simi1505/60W-2m-FM-TRX-OE3SDE/1W FM TRX DRA818V/Eagle Files/1W_FM_TRX_DRA818V_Pics/1W FM TRX DRA818V_Drills.png

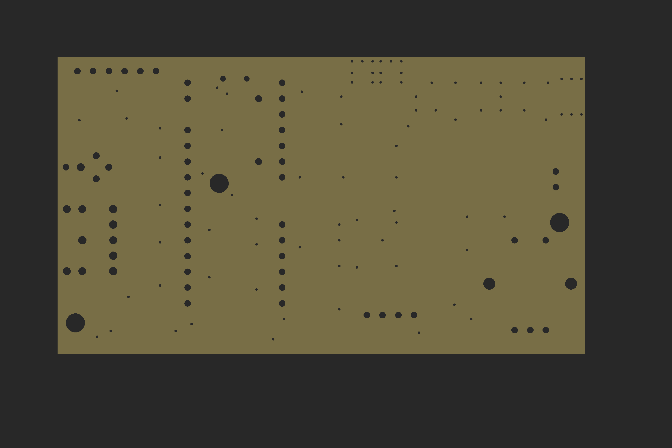
1W FM TRX DRA818V/Eagle Files/1W_FM_TRX_DRA818V_Pics/1W FM TRX DRA818V_Drills.png
