simi1505/60W-2m-FM-TRX-OE3SDE/60W FM PA RA60H1317M1A/Eagle Files/60W_FM_PA_Pics/60W_FM_PA_Drills.png

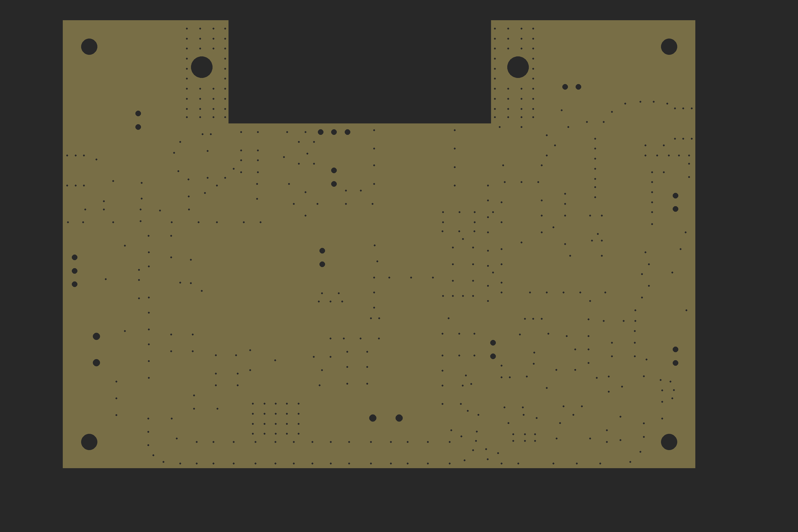
60W FM PA RA60H1317M1A/Eagle Files/60W_FM_PA_Pics/60W_FM_PA_Drills.png
