simi1505/60W-2m-FM-TRX-OE3SDE/60W FM PA RA60H1317M1A/Simulation/Elsie/LC-BP-IN/BPF1_Circuit.PNG

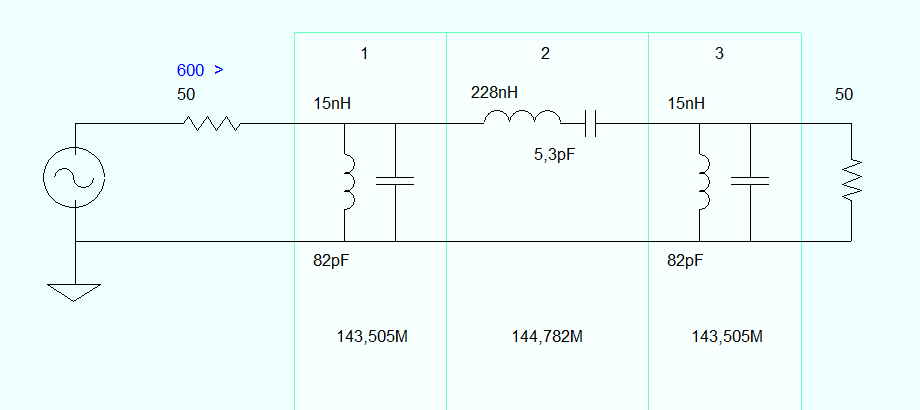
60W FM PA RA60H1317M1A/Simulation/Elsie/LC-BP-IN/BPF1_Circuit.PNG
