simi1505/60W-2m-FM-TRX-OE3SDE/60W FM PA RA60H1317M1A/Simulation/Elsie/LC-LP-OUT/LC-LP-OUT_Circuit.PNG

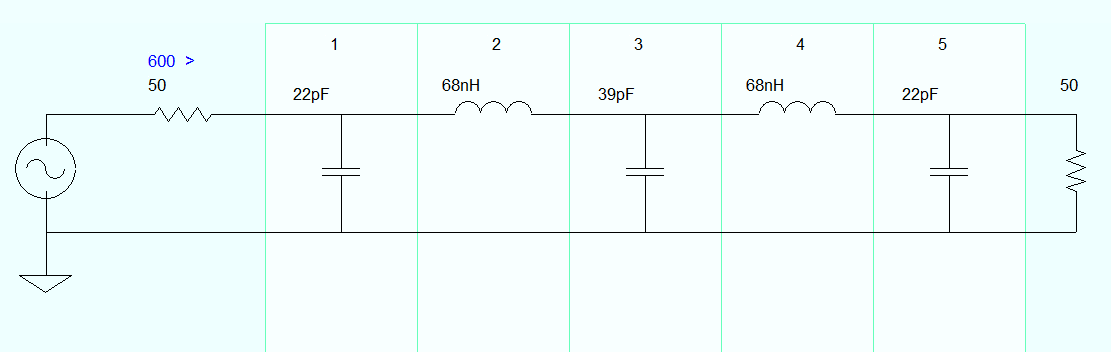
60W FM PA RA60H1317M1A/Simulation/Elsie/LC-LP-OUT/LC-LP-OUT_Circuit.PNG
