simi1505/60W-2m-FM-TRX-OE3SDE/60W FM PA RA60H1317M1A/Simulation/LTSpice/LC-LP-OUT/LC-LP_OUT.PNG

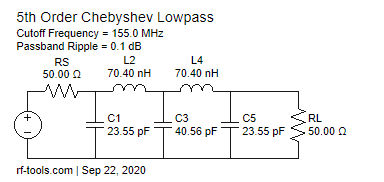
60W FM PA RA60H1317M1A/Simulation/LTSpice/LC-LP-OUT/LC-LP_OUT.PNG
