simi1505/60W-2m-FM-TRX-OE3SDE/60W FM PA RA60H1317M1A/Documentation/8_result/fig/result_2.jpg

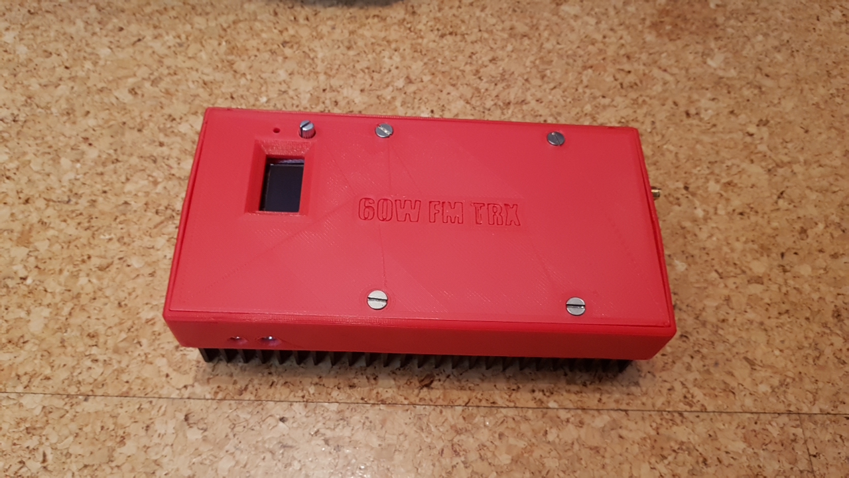
60W FM PA RA60H1317M1A/Documentation/8_result/fig/result_2.jpg
