simi1505/60W-2m-FM-TRX-OE3SDE/60W FM PA RA60H1317M1A/Documentation/8_result/fig/WhatsApp Image 2021-08-19 at 13.19.44 (3).jpeg

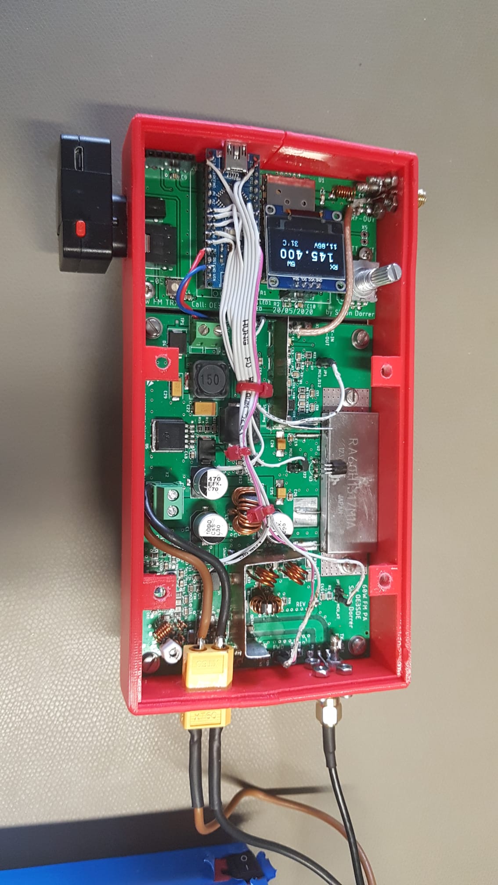
60W FM PA RA60H1317M1A/Documentation/8_result/fig/WhatsApp Image 2021-08-19 at 13.19.44 (3).jpeg
