simi1505/60W-2m-FM-TRX-OE3SDE/60W FM PA RA60H1317M1A/Measurements/TX-Path/57dBmOUT.png

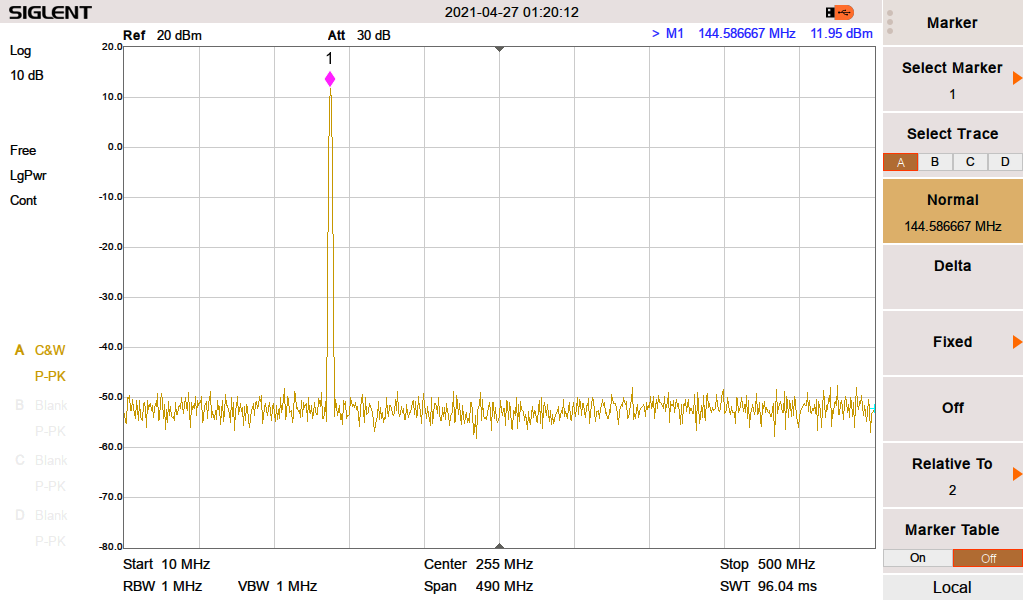
60W FM PA RA60H1317M1A/Measurements/TX-Path/57dBmOUT.png
