simi1505/60W-2m-FM-TRX-OE3SDE/60W FM PA RA60H1317M1A/Simulation/LTSpice/LC-LP-IN/LC-LP-IN.asc

C1: cap; 22pF
C2: cap; 43pF
C3: cap; 43pF
C4: cap; 22pF
L1: ind; 68nH
L2: ind; 82nH
L3: ind; 68nH
R1: res; 50
R2: res; 50
V1: voltage; SINE(); AC 1
Named nets: 0
.ac dec 1000 100Meg 400Meg
