simi1505/60W-2m-FM-TRX-OE3SDE/60W FM PA RA60H1317M1A/Simulation/LTSpice/VGG/VGG.asc

C1: cap; 100nF
C4: cap; 100nF
D1: diode; 1N4148
D2: diode; 1N4148
D3: diode; 1N4148
D4: diode; 1N4148
Q1: npn; 2N3904
Q2: pnp; BC557B
R1: res; 1k
R2: res; 100
R5: res; 1k
R6: res; 1
R7: res; 999
R8: res; 220
R9: res; 100
R10: res; 10k
V1: voltage; 0
V3: voltage; 13.8
Named nets: 0
.tran 0 1 0
